jzdziarski/jamma/Renderings/atari_system_pcb.png

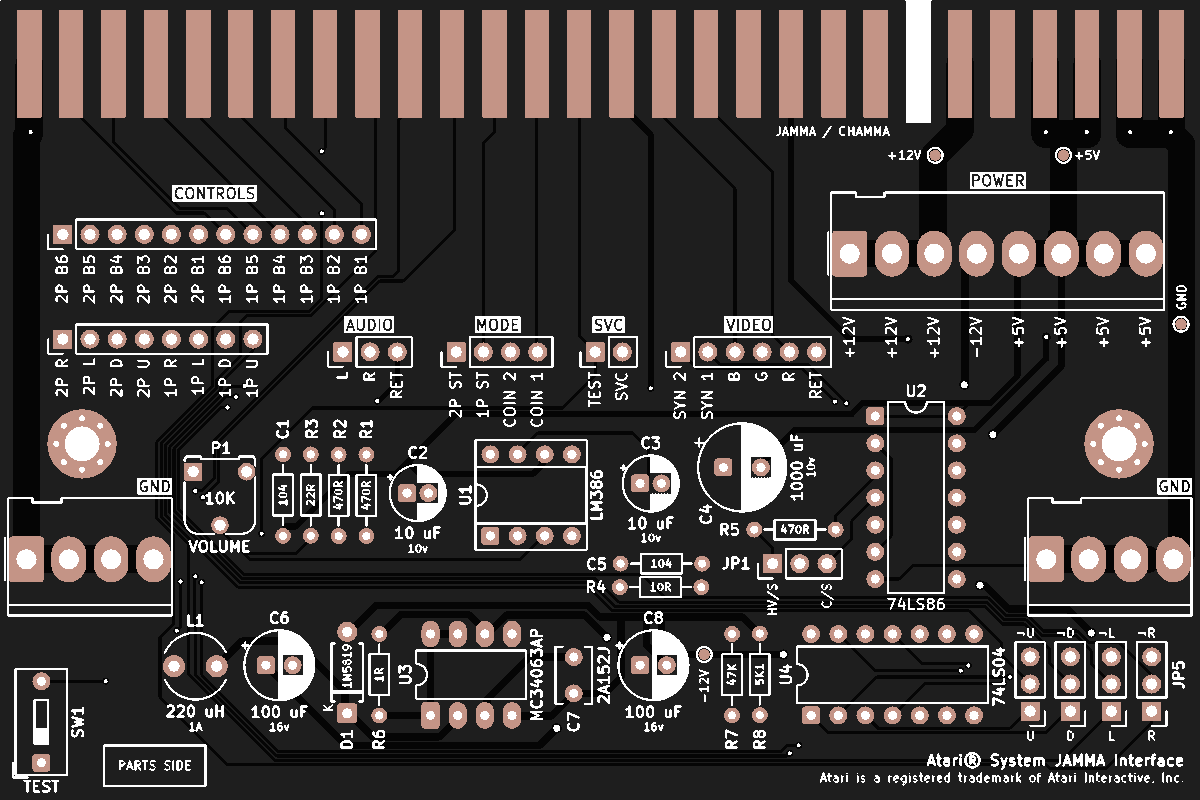
Renderings/atari_system_pcb.png
