jzdziarski/jamma/Renderings/outrun_pcb.png

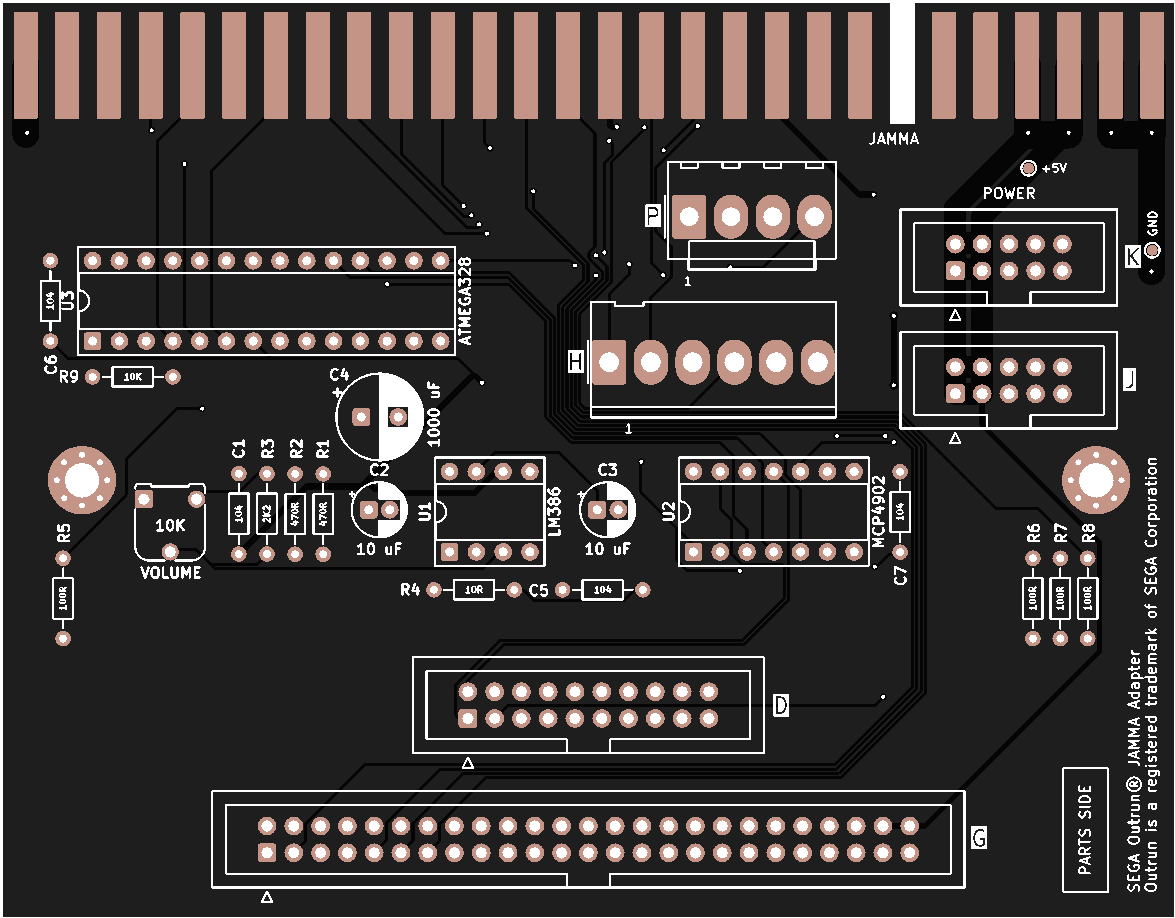
Renderings/outrun_pcb.png
