jzdziarski/jamma/Renderings/roadblasters_pcb.png

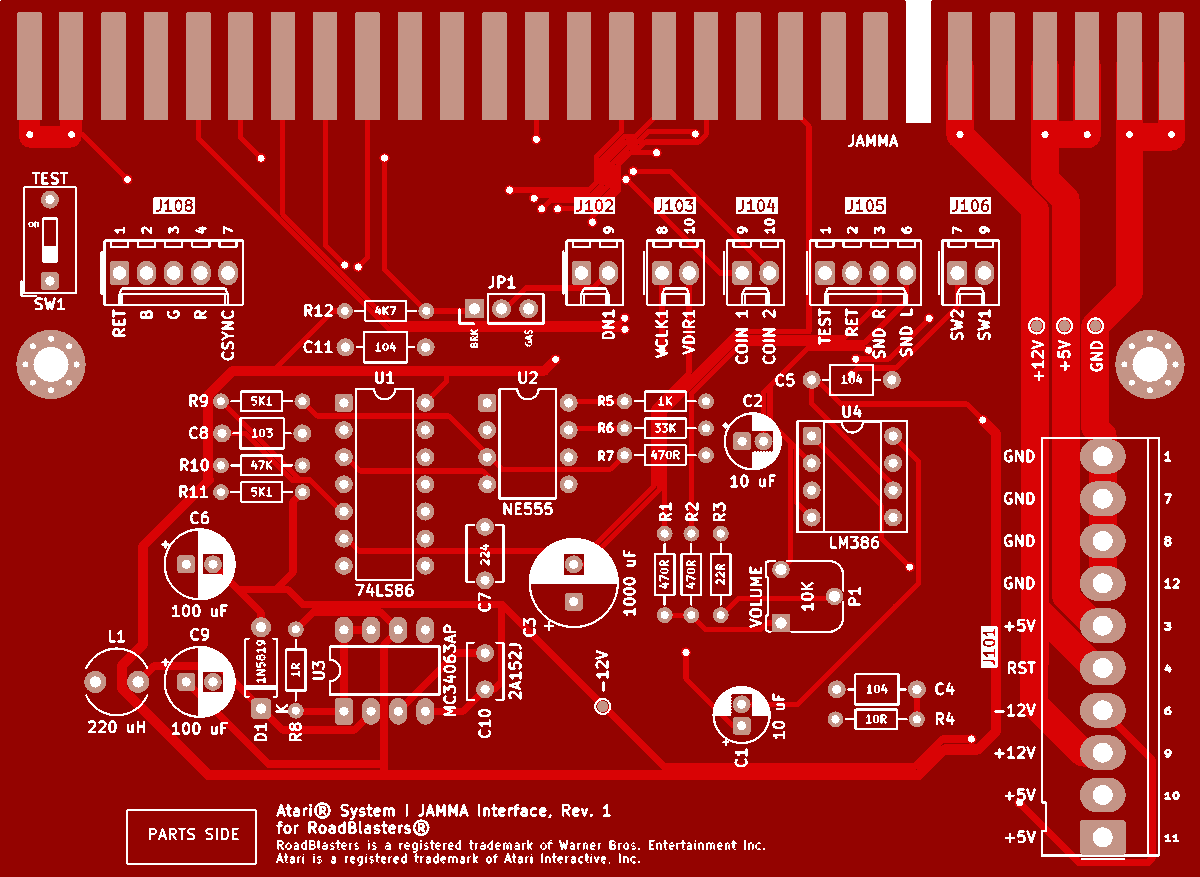
Renderings/roadblasters_pcb.png
