jzdziarski/jamma/Renderings/tron_pcb.png

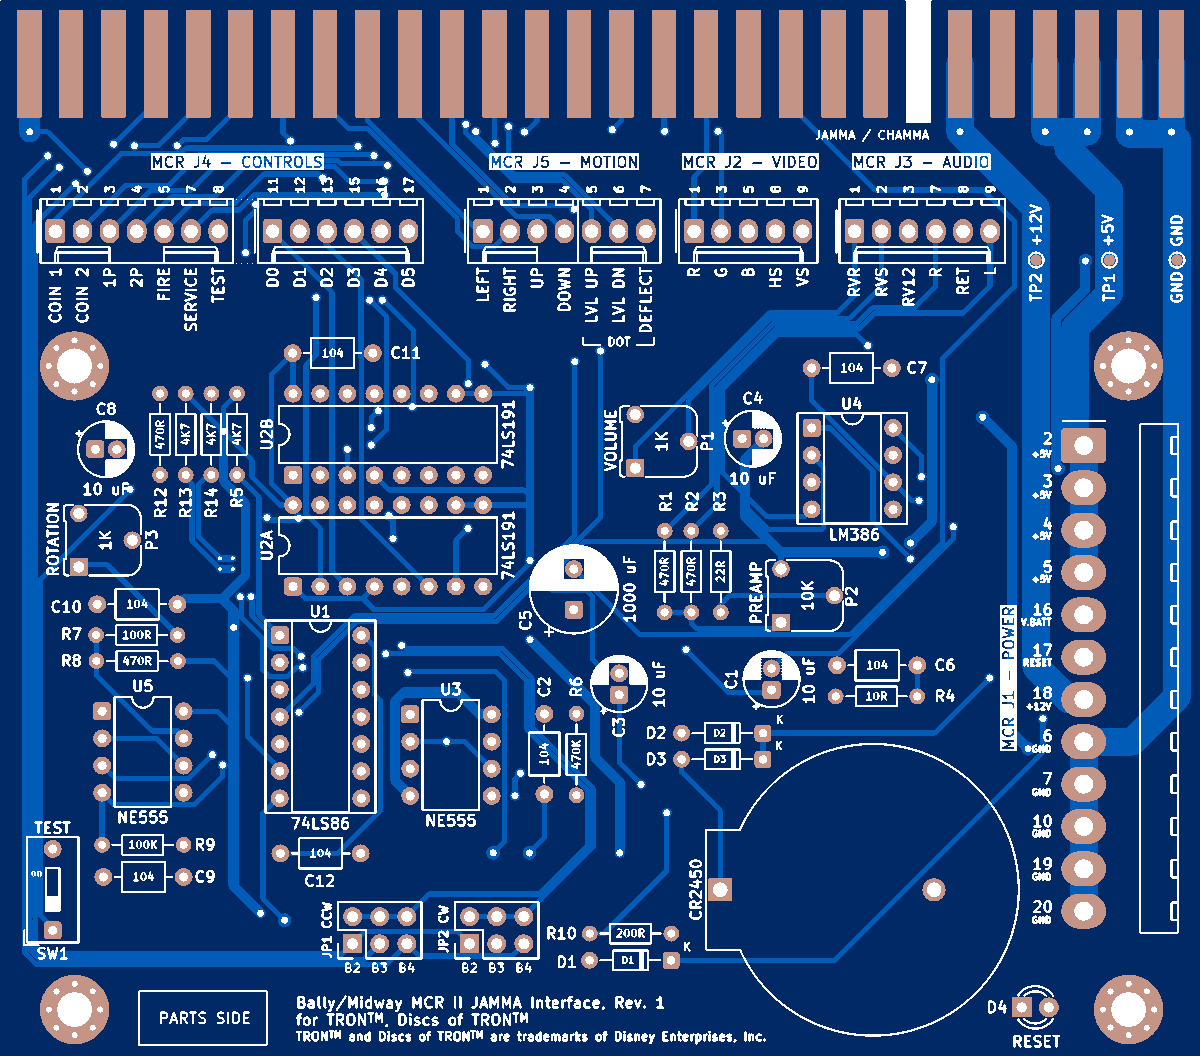
Renderings/tron_pcb.png
